adamf/Moros/shield/KiCad/3d_models/ab2_usb/stl/AB2_USB_MICRO_SMD.stl

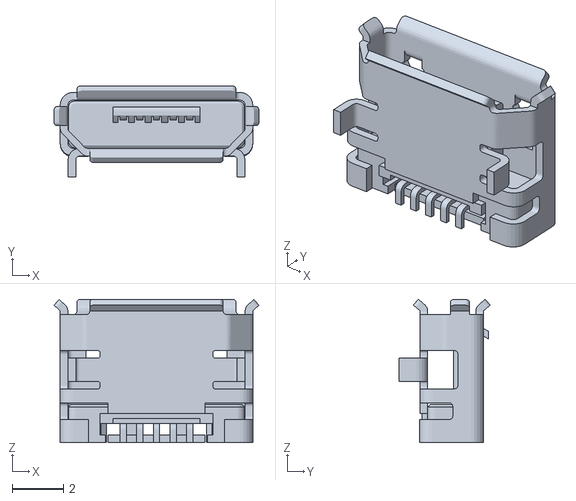
[picture p20: CAD file, 2014-12-30]
shield/KiCad/3d_models/ab2_usb/stl/AB2_USB_MICRO_SMD.stl
8.00 x 3.57 x 5.60
