adamf/Moros/shield/KiCad/3d_models/ab2_xtal/stl/AB2_XTAL_5.2x1.45x1.45MM.stl

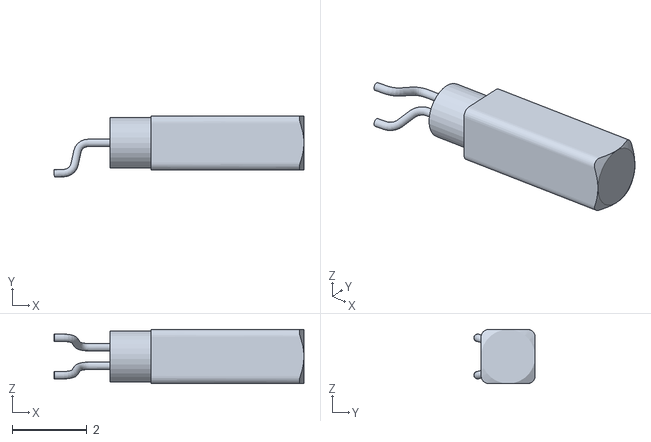
[picture p21: CAD file, 2014-12-30]
shield/KiCad/3d_models/ab2_xtal/stl/AB2_XTAL_5.2x1.45x1.45MM.stl
6.70 x 1.65 x 1.45
