adamf/Moros/shield/KiCad/3d_models/ab2_connector/stl/AB2_TRS_3p5MM_PTH_WINGS3D.stl

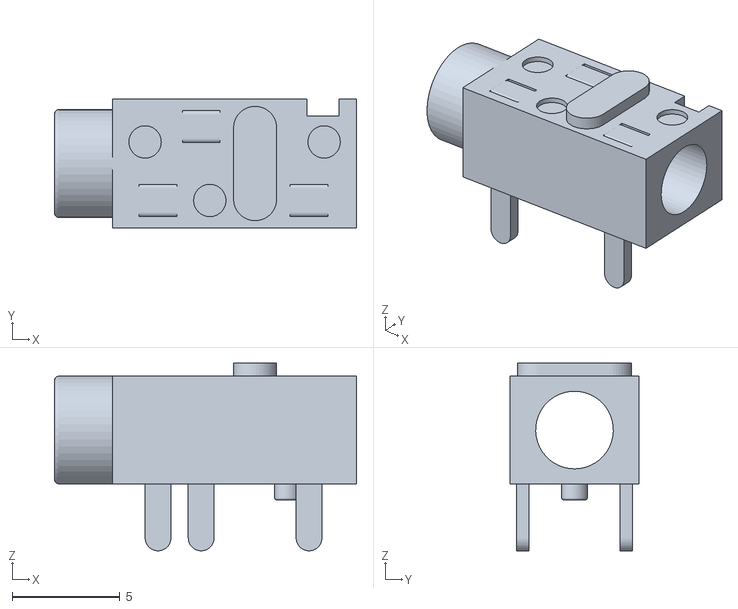
[picture p22: CAD file, 2014-12-30]
shield/KiCad/3d_models/ab2_connector/stl/AB2_TRS_3p5MM_PTH_WINGS3D.stl
14.0 x 6.00 x 8.70
