adamf/Moros/shield/KiCad/3d_models/ab2_header/stl/AB2_HDR_M01-1H_WINGS3D.stl

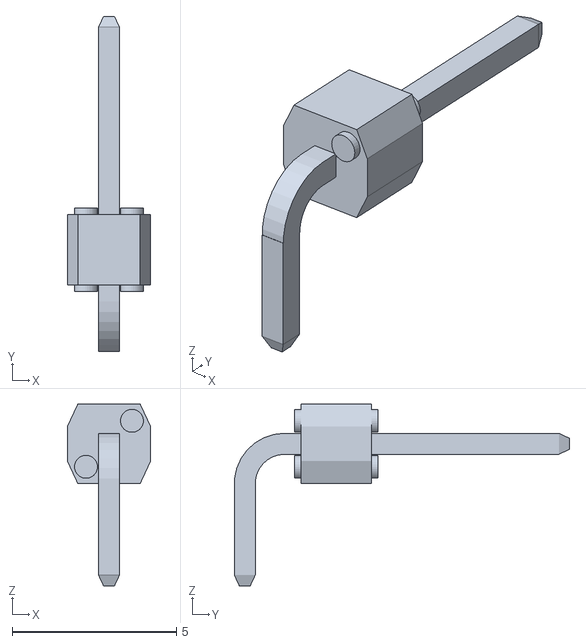
[picture p23: CAD file, 2014-12-30]
shield/KiCad/3d_models/ab2_header/stl/AB2_HDR_M01-1H_WINGS3D.stl
2.54 x 10.2 x 5.54
