adamf/Moros/shield/KiCad/3d_models/ab2_holesnpoles/stl/AB2_FR4_1.96x1.96INx1.6MM_ROUNDED_WINGS3D.stl

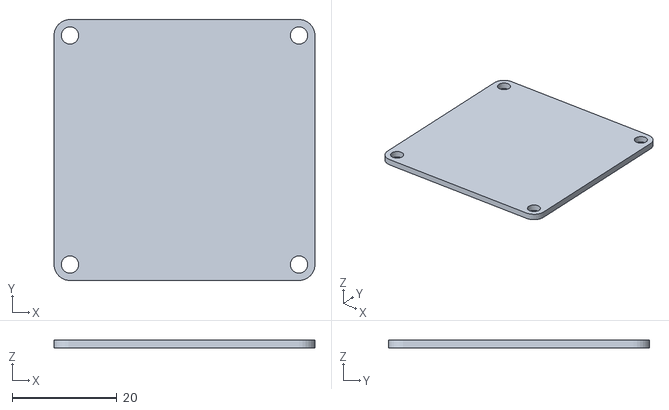
[picture p24: CAD file, 2014-12-30]
shield/KiCad/3d_models/ab2_holesnpoles/stl/AB2_FR4_1.96x1.96INx1.6MM_ROUNDED_WINGS3D.stl
49.8 x 49.8 x 1.55
