adamf/Moros/shield/KiCad/3d_models/ab2_input_devices/stl/AB2_PB_MOM_5.2MM_SMD.stl

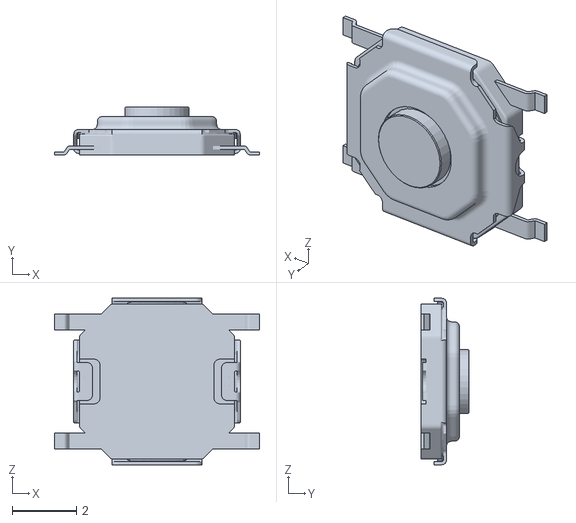
[picture p26: CAD file, 2014-12-30]
shield/KiCad/3d_models/ab2_input_devices/stl/AB2_PB_MOM_5.2MM_SMD.stl
6.40 x 1.50 x 5.20
