adamf/Moros/shield/KiCad/3d_models/ab2_lqfp/stl/AB2_LQFP80_WINGS3D.stl

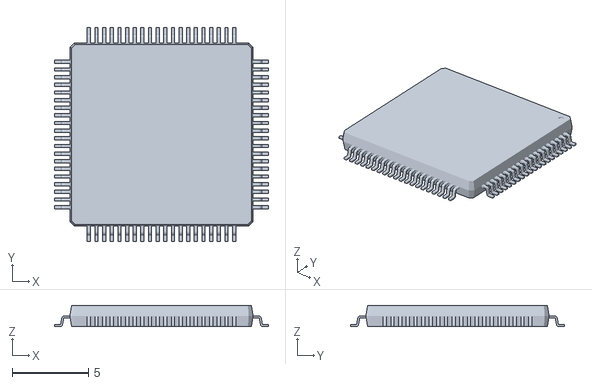
[picture p27: CAD file, 2014-12-30]
shield/KiCad/3d_models/ab2_lqfp/stl/AB2_LQFP80_WINGS3D.stl
14.0 x 14.0 x 1.40
