adamf/Moros/shield/KiCad/3d_models/ab2_power/stl/AB2_90DEG_4MM_JACK_PTH_WINGS3D.stl

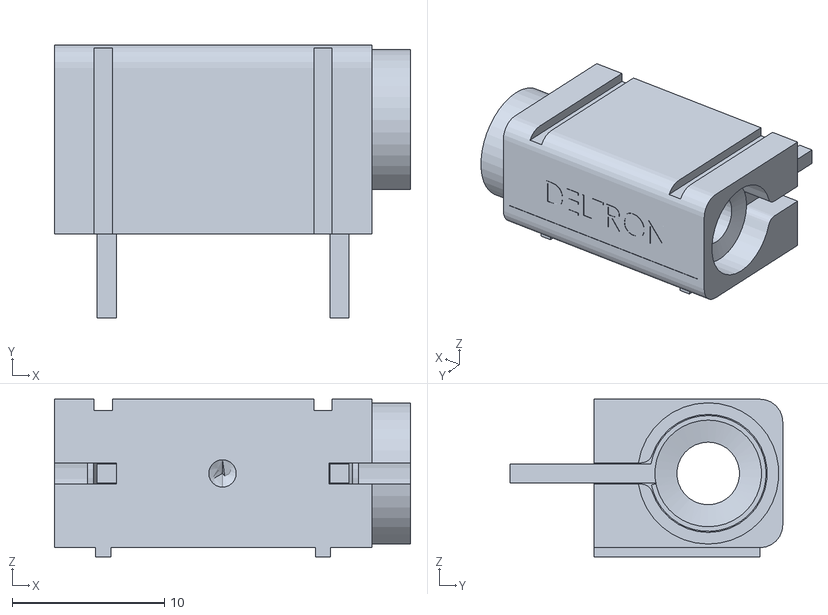
[picture p29: CAD file, 2014-12-30]
shield/KiCad/3d_models/ab2_power/stl/AB2_90DEG_4MM_JACK_PTH_WINGS3D.stl
23.4 x 17.9 x 10.4
