adamf/Moros/shield/KiCad/3d_models/ab2_usb/stl/AB2_USB_MINI_SMD.stl

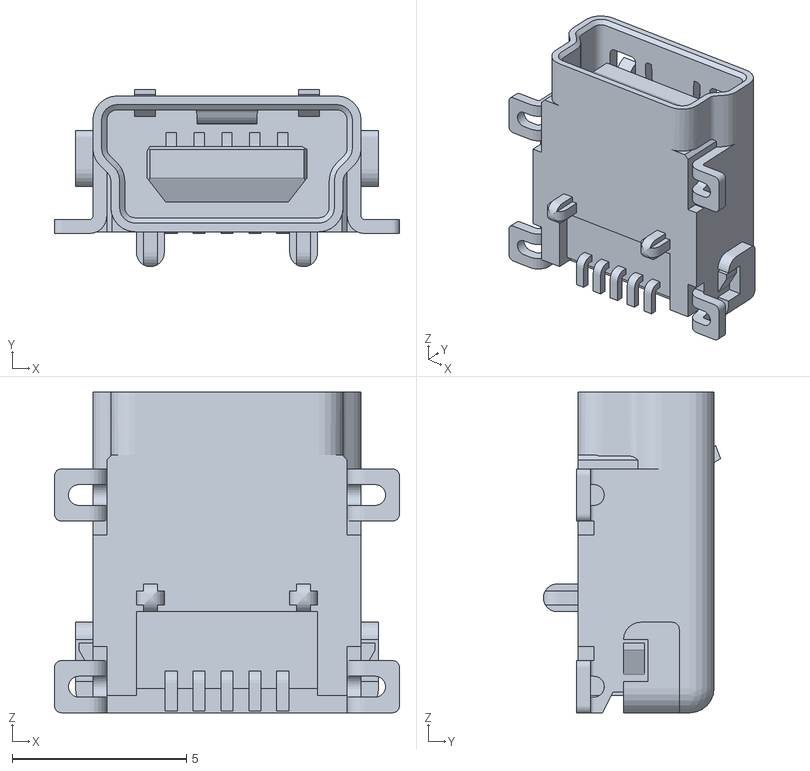
[picture p31: CAD file, 2014-12-30]
shield/KiCad/3d_models/ab2_usb/stl/AB2_USB_MINI_SMD.stl
9.90 x 5.09 x 9.20
