adamf/Moros/shield/KiCad/3d_models/ab2_7seg/stl/AB2_7SEG_5IN_H_WINGS3D.stl

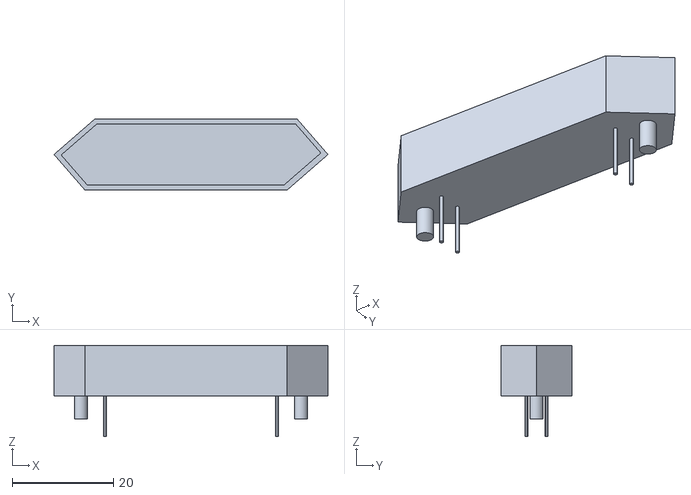
[picture p32: CAD file, 2014-12-30]
shield/KiCad/3d_models/ab2_7seg/stl/AB2_7SEG_5IN_H_WINGS3D.stl
54.1 x 14.0 x 18.0
