adamf/Moros/shield/KiCad/3d_models/ab2_connector/stl/AB2_DB25_F_RA.stl

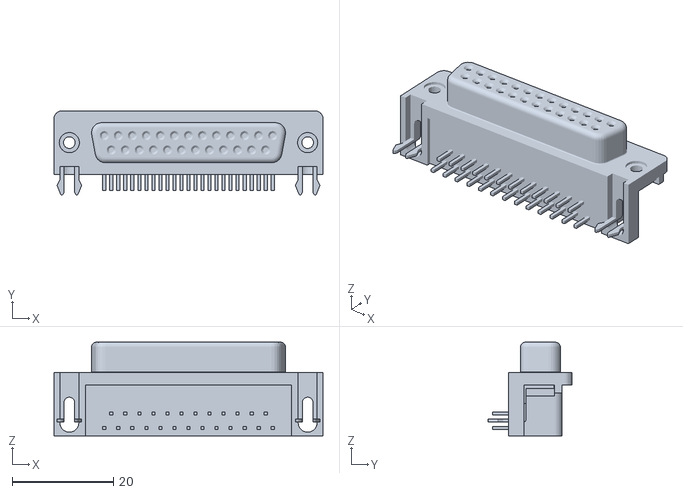
[picture p33: CAD file, 2014-12-30]
shield/KiCad/3d_models/ab2_connector/stl/AB2_DB25_F_RA.stl
53.1 x 16.6 x 18.5
