adamf/Moros/shield/KiCad/3d_models/ab2_holesnpoles/stl/AB2_FR4_1.96x0.94INx1.6MM_ROUNDED_WINGS3D.stl

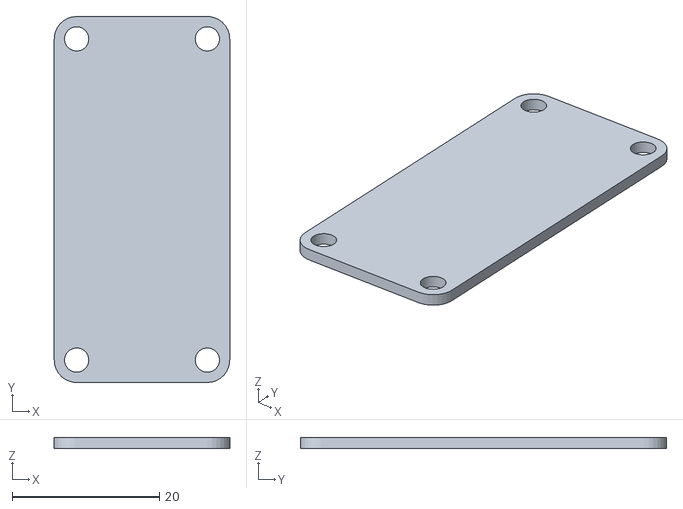
[picture p34: CAD file, 2014-12-30]
shield/KiCad/3d_models/ab2_holesnpoles/stl/AB2_FR4_1.96x0.94INx1.6MM_ROUNDED_WINGS3D.stl
23.9 x 49.8 x 1.55
