adamf/Moros/shield/KiCad/3d_models/ab2_idc/stl/AB2_HDR_M04-2V-S-TE_WINGS3D.stl

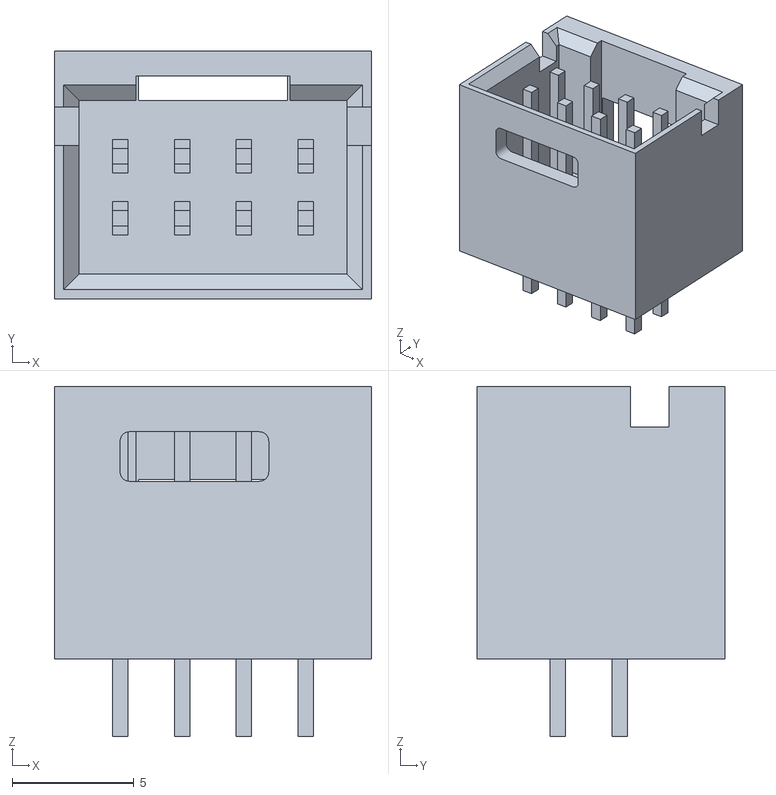
[picture p35: CAD file, 2014-12-30]
shield/KiCad/3d_models/ab2_idc/stl/AB2_HDR_M04-2V-S-TE_WINGS3D.stl
13.0 x 10.2 x 14.4
