adamf/Moros/shield/KiCad/3d_models/ab2_input_devices/stl/AB2_DIP_SW04_PIANO_PTH.stl

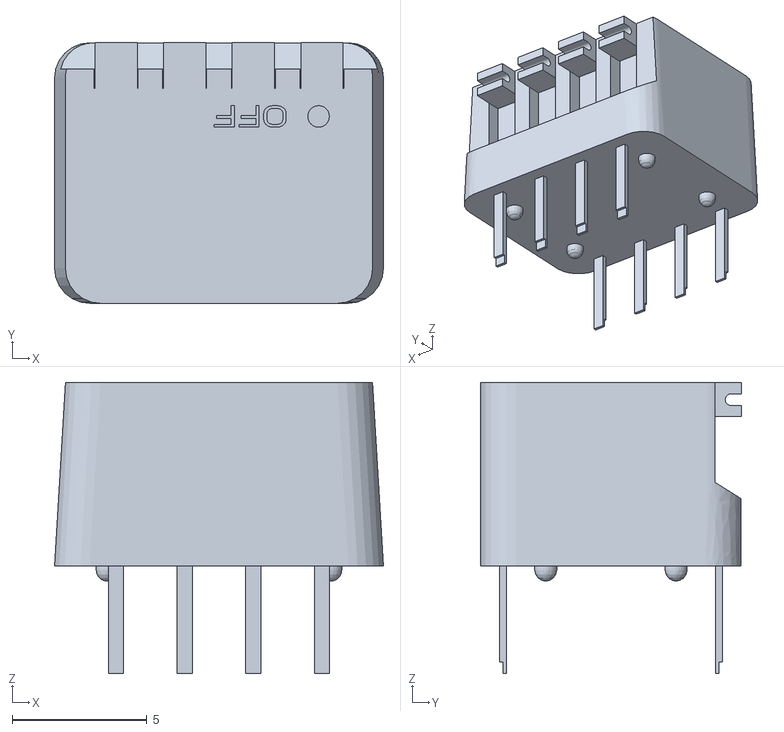
[picture p36: CAD file, 2014-12-30]
shield/KiCad/3d_models/ab2_input_devices/stl/AB2_DIP_SW04_PIANO_PTH.stl
12.2 x 9.65 x 10.8
