adamf/Moros/shield/KiCad/3d_models/ab2_lqfp/stl/AB2_LQFP64_WINGS3D.stl

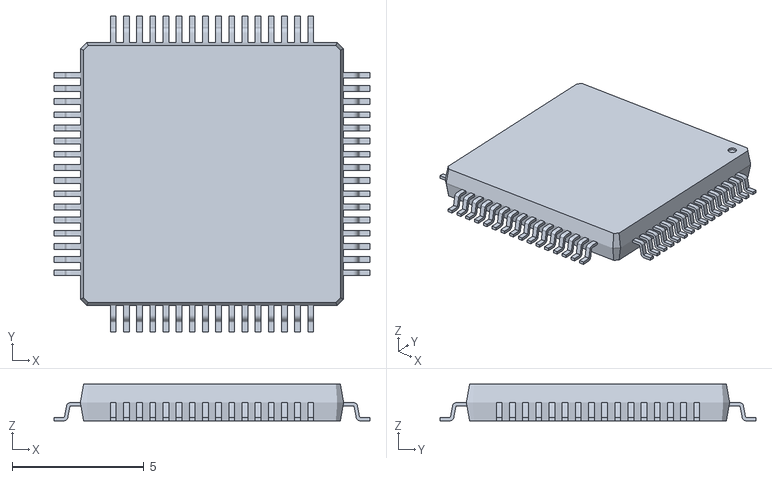
[picture p37: CAD file, 2014-12-30]
shield/KiCad/3d_models/ab2_lqfp/stl/AB2_LQFP64_WINGS3D.stl
12.0 x 12.0 x 1.40
