adamf/Moros/shield/KiCad/3d_models/ab2_passive/stl/AB2_0805_C_60_WINGS3D.stl

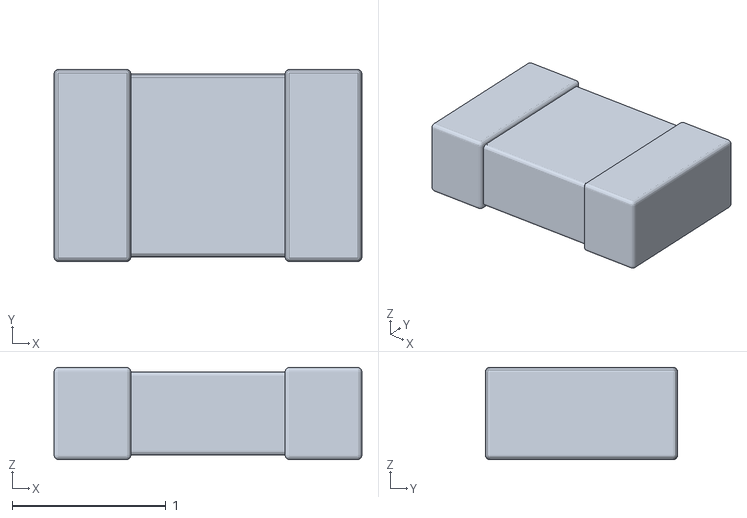
[picture p38: CAD file, 2014-12-30]
shield/KiCad/3d_models/ab2_passive/stl/AB2_0805_C_60_WINGS3D.stl
2.00 x 1.25 x 0.6
