adamf/Moros/shield/KiCad/3d_models/ab2_so/stl/AB2_SO16_WINGS3D.stl

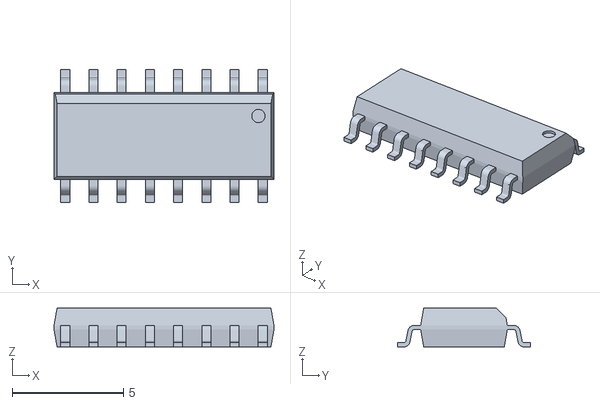
[picture p39: CAD file, 2014-12-30]
shield/KiCad/3d_models/ab2_so/stl/AB2_SO16_WINGS3D.stl
9.90 x 6.00 x 1.75
