adamf/Moros/shield/KiCad/3d_models/ab2_7seg/stl/AB2_7SEG_5IN_DEC_WINGS3D.stl

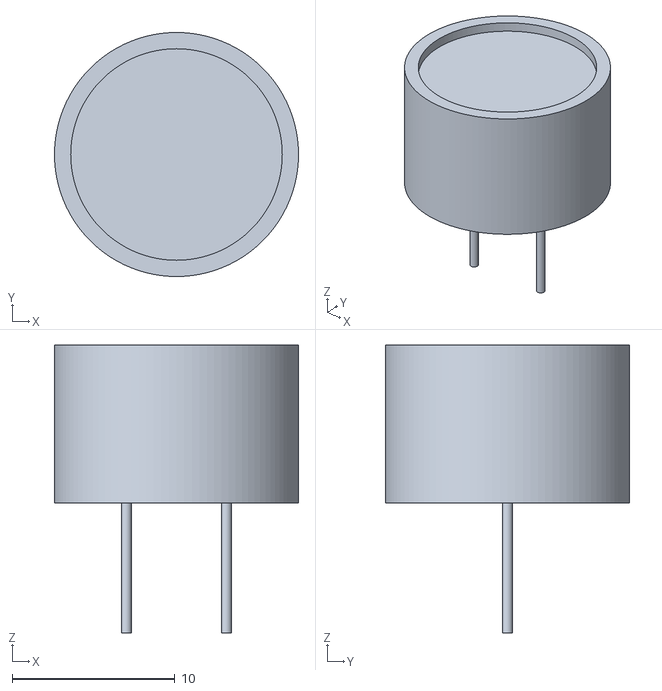
[picture p40: CAD file, 2014-12-30]
shield/KiCad/3d_models/ab2_7seg/stl/AB2_7SEG_5IN_DEC_WINGS3D.stl
15.0 x 15.0 x 17.7
