adamf/Moros/shield/KiCad/3d_models/ab2_connector/stl/AB2_RJ45_VERT_UNSHIELDED.stl

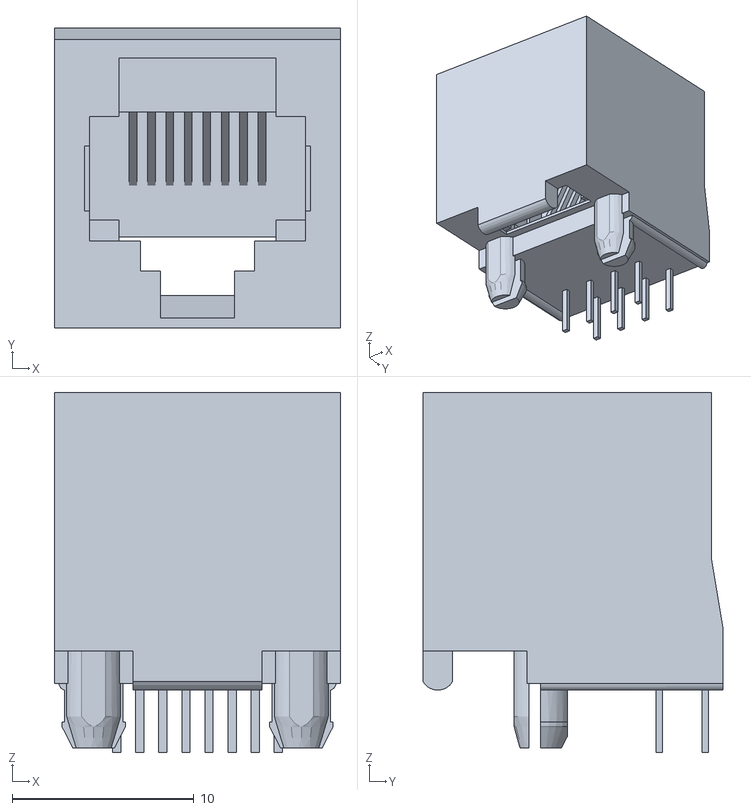
[picture p41: CAD file, 2014-12-30]
shield/KiCad/3d_models/ab2_connector/stl/AB2_RJ45_VERT_UNSHIELDED.stl
15.7 x 16.5 x 19.8
