adamf/Moros/shield/KiCad/3d_models/ab2_idc/stl/AB2_HDR_M07-2V-S-TE_WINGS3D.stl

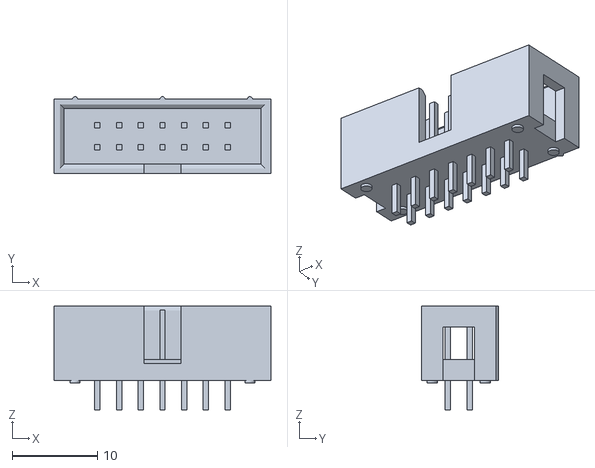
[picture p42: CAD file, 2014-12-30]
shield/KiCad/3d_models/ab2_idc/stl/AB2_HDR_M07-2V-S-TE_WINGS3D.stl
25.4 x 9.00 x 12.1
