adamf/Moros/shield/KiCad/3d_models/ab2_input_devices/stl/AB2_PB_MOM_6MM_PTH_BLK.stl

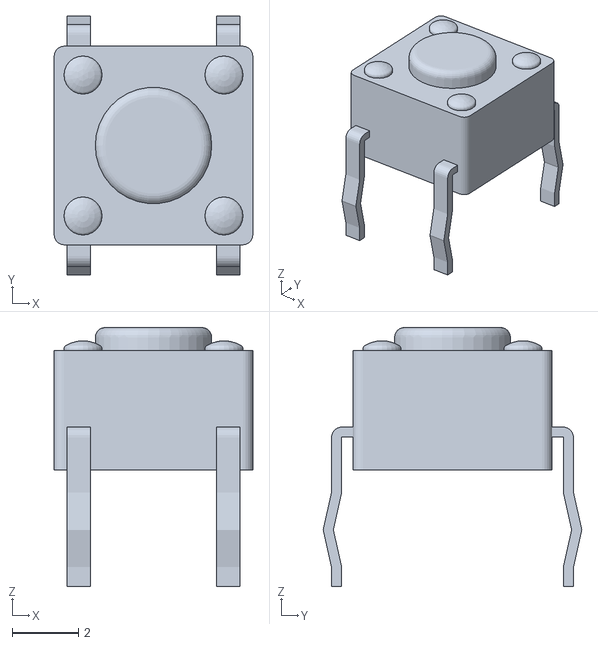
[picture p43: CAD file, 2014-12-30]
shield/KiCad/3d_models/ab2_input_devices/stl/AB2_PB_MOM_6MM_PTH_BLK.stl
5.99 x 7.80 x 7.81
