adamf/Moros/shield/KiCad/3d_models/ab2_lqfp/stl/AB2_LQFP100_WINGS3D.stl

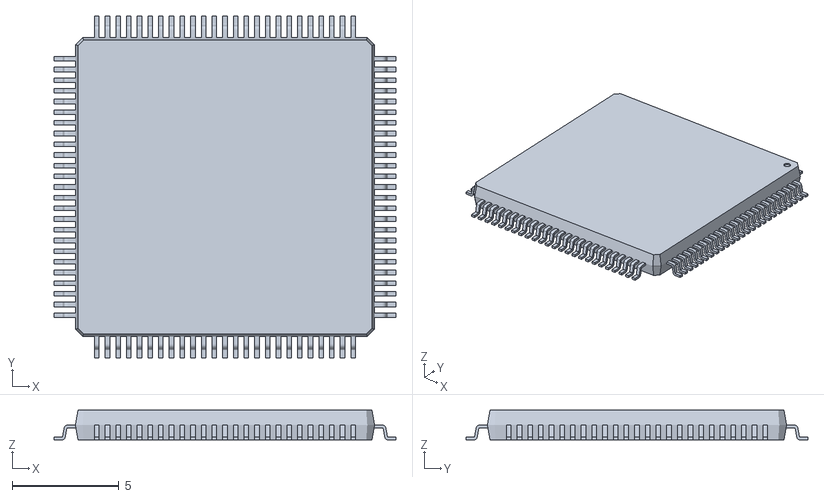
[picture p44: CAD file, 2014-12-30]
shield/KiCad/3d_models/ab2_lqfp/stl/AB2_LQFP100_WINGS3D.stl
16.0 x 16.0 x 1.40
