adamf/Moros/shield/KiCad/3d_models/ab2_passive/stl/AB2_L_RADIAL_8.7x12x5MM_SHORT_WINGS3D.stl

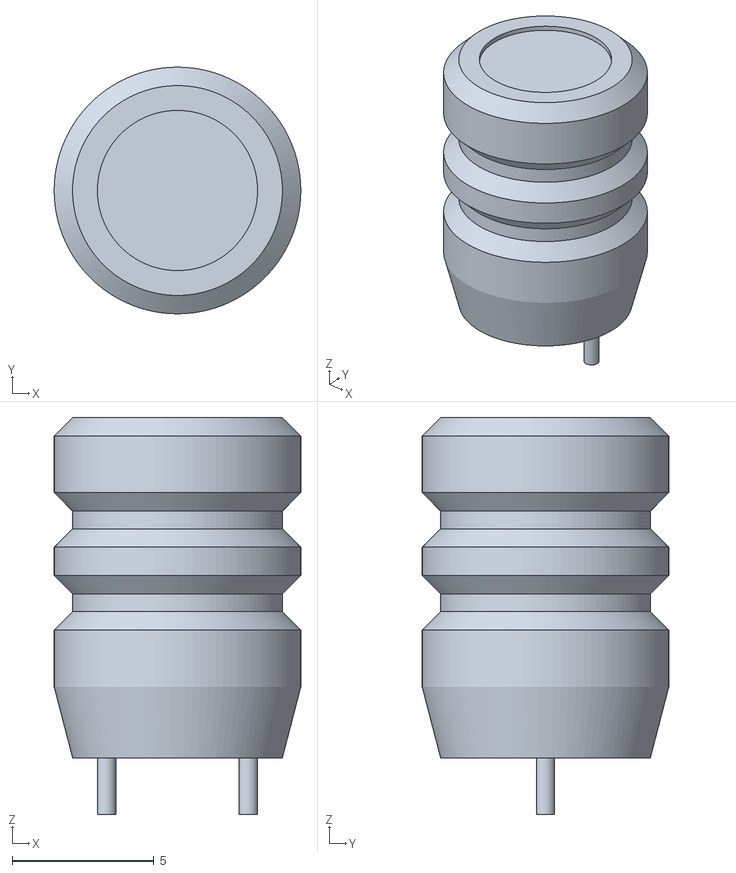
[picture p45: CAD file, 2014-12-30]
shield/KiCad/3d_models/ab2_passive/stl/AB2_L_RADIAL_8.7x12x5MM_SHORT_WINGS3D.stl
8.70 x 8.70 x 14.0
