adamf/Moros/shield/KiCad/3d_models/ab2_holesnpoles/stl/AB2_FR4_3.92x3.92INx1.6MM_ROUNDED_WINGS3D.stl

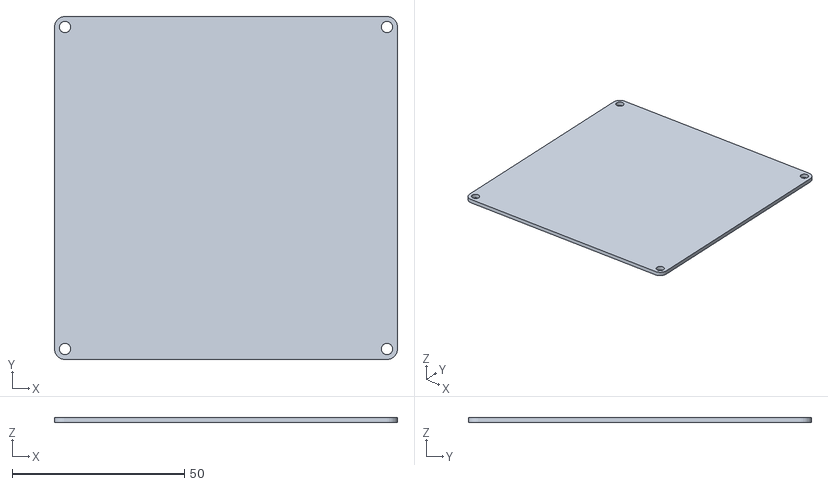
[picture p47: CAD file, 2014-12-30]
shield/KiCad/3d_models/ab2_holesnpoles/stl/AB2_FR4_3.92x3.92INx1.6MM_ROUNDED_WINGS3D.stl
99.6 x 99.6 x 1.55
