adamf/Moros/shield/KiCad/3d_models/ab2_idc/stl/AB2_HDR_M17-2V-S-OMRON.stl

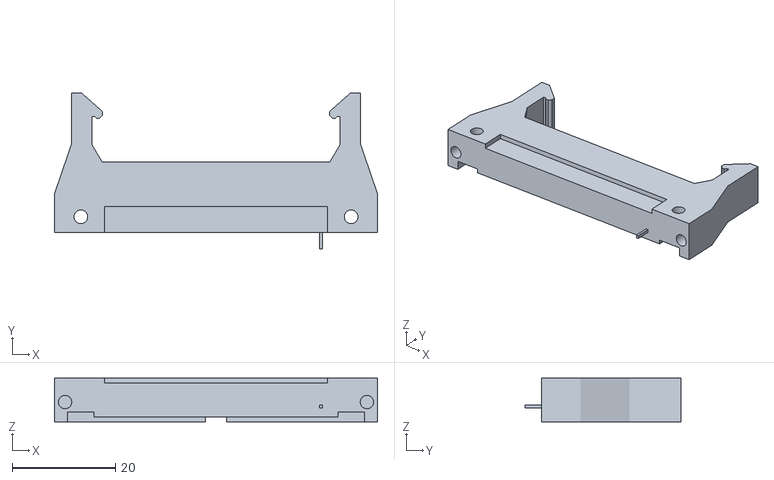
[picture p48: CAD file, 2014-12-30]
shield/KiCad/3d_models/ab2_idc/stl/AB2_HDR_M17-2V-S-OMRON.stl
62.5 x 30.2 x 8.50
