adamf/Moros/shield/KiCad/3d_models/ab2_lqfp/stl/AB2_LQFP32_WINGS3D.stl

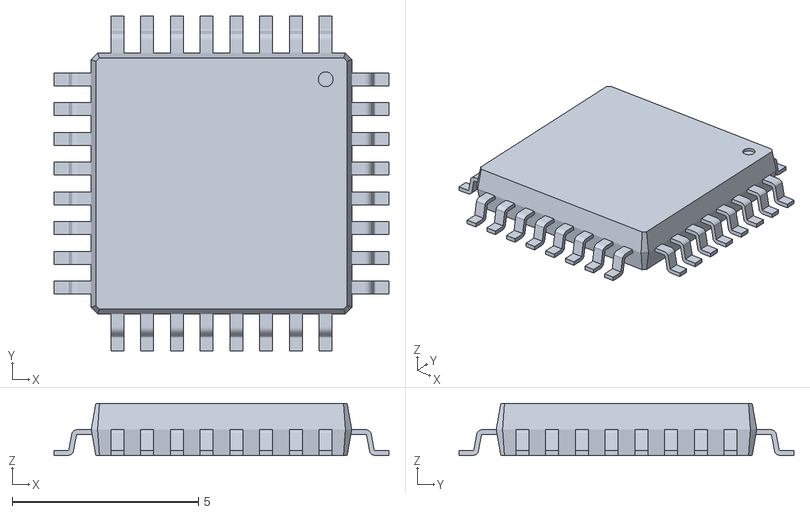
[picture p49: CAD file, 2014-12-30]
shield/KiCad/3d_models/ab2_lqfp/stl/AB2_LQFP32_WINGS3D.stl
9.00 x 9.00 x 1.40
