adamf/Moros/shield/KiCad/3d_models/ab2_passive/stl/AB2_1206_C_115_WINGS3D.stl

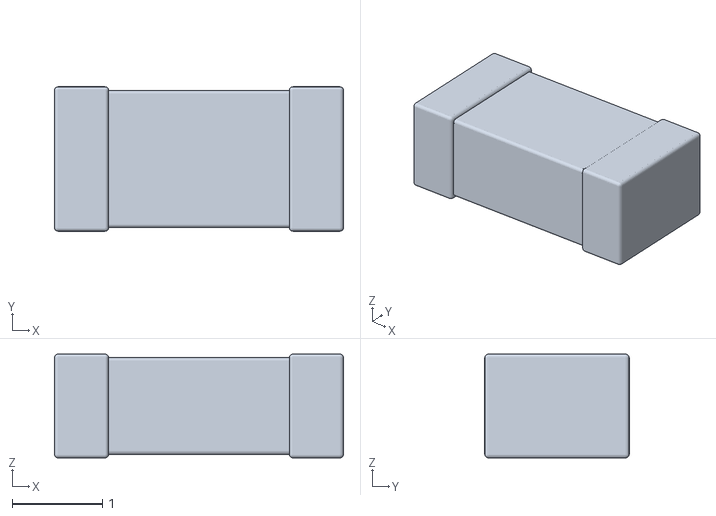
[picture p50: CAD file, 2014-12-30]
shield/KiCad/3d_models/ab2_passive/stl/AB2_1206_C_115_WINGS3D.stl
3.20 x 1.60 x 1.15
