adamf/Moros/shield/KiCad/3d_models/ab2_7seg/stl/AB2_7_SEG_8IN_DEC_WINGS3D.stl

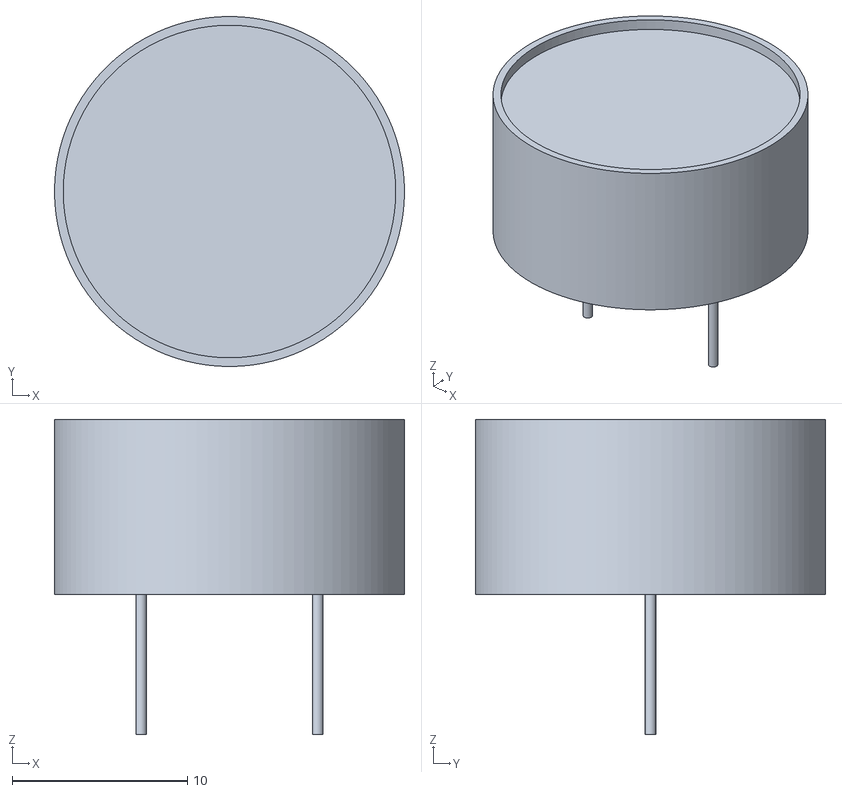
[picture p52: CAD file, 2014-12-30]
shield/KiCad/3d_models/ab2_7seg/stl/AB2_7_SEG_8IN_DEC_WINGS3D.stl
20.0 x 20.0 x 18.0
