adamf/Moros/shield/KiCad/3d_models/ab2_idc/stl/AB2_HDR_M05-2V-S-TE_WINGS3D.stl

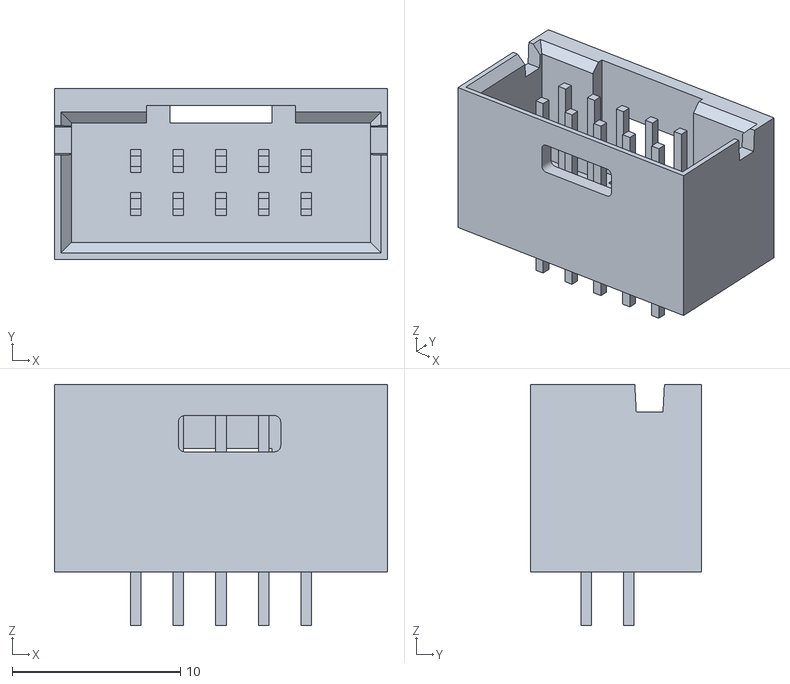
[picture p53: CAD file, 2014-12-30]
shield/KiCad/3d_models/ab2_idc/stl/AB2_HDR_M05-2V-S-TE_WINGS3D.stl
19.8 x 10.2 x 14.4
