adamf/Moros/shield/KiCad/3d_models/ab2_lqfp/stl/AB2_LQFP128_WINGS3D.stl

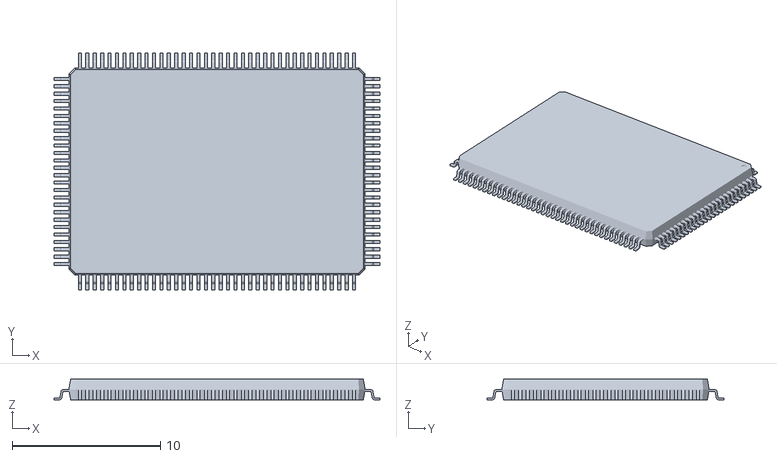
[picture p54: CAD file, 2014-12-30]
shield/KiCad/3d_models/ab2_lqfp/stl/AB2_LQFP128_WINGS3D.stl
22.0 x 16.0 x 1.40
