adamf/Moros/shield/KiCad/3d_models/ab2_passive/stl/AB2_DO-214AC_WINGS3D.stl

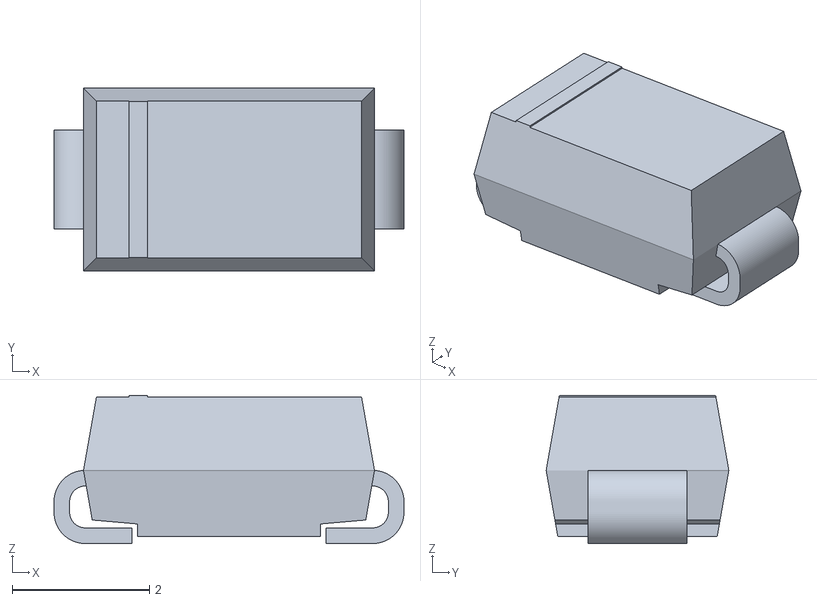
[picture p55: CAD file, 2014-12-30]
shield/KiCad/3d_models/ab2_passive/stl/AB2_DO-214AC_WINGS3D.stl
5.11 x 2.66 x 2.16
