adamf/Moros/shield/KiCad/3d_models/ab2_so/stl/AB2_SO18_W_WINGS3D.stl

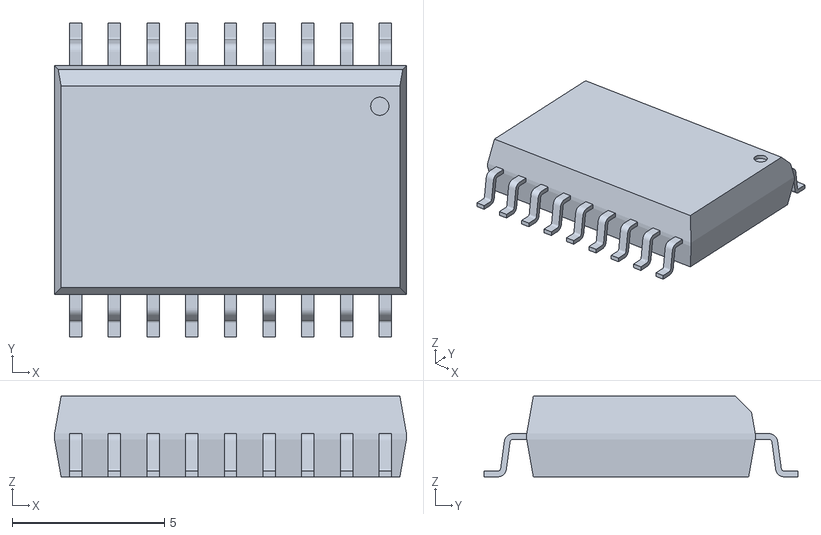
[picture p56: CAD file, 2014-12-30]
shield/KiCad/3d_models/ab2_so/stl/AB2_SO18_W_WINGS3D.stl
11.6 x 10.3 x 2.65
