adamf/Moros/shield/KiCad/3d_models/ab2_idc/stl/AB2_HDR_M03-2V-S-3M_WINGS3D.stl

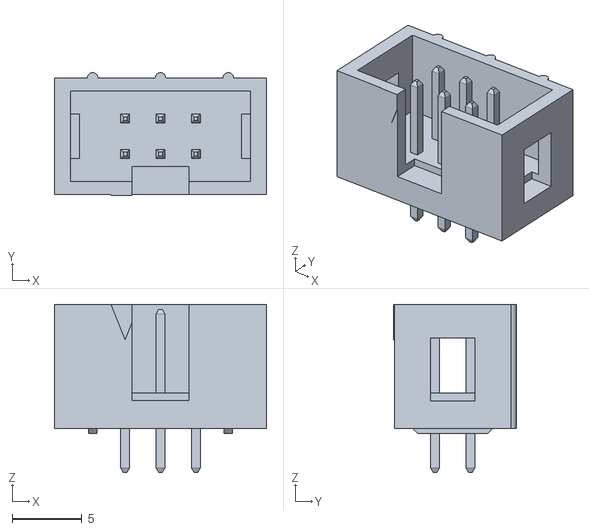
[picture p57: CAD file, 2014-12-30]
shield/KiCad/3d_models/ab2_idc/stl/AB2_HDR_M03-2V-S-3M_WINGS3D.stl
15.2 x 8.81 x 12.1
