adamf/Moros/shield/KiCad/3d_models/ab2_passive/stl/AB2_PLCC6_LED_ROUND_WINGS3D.stl

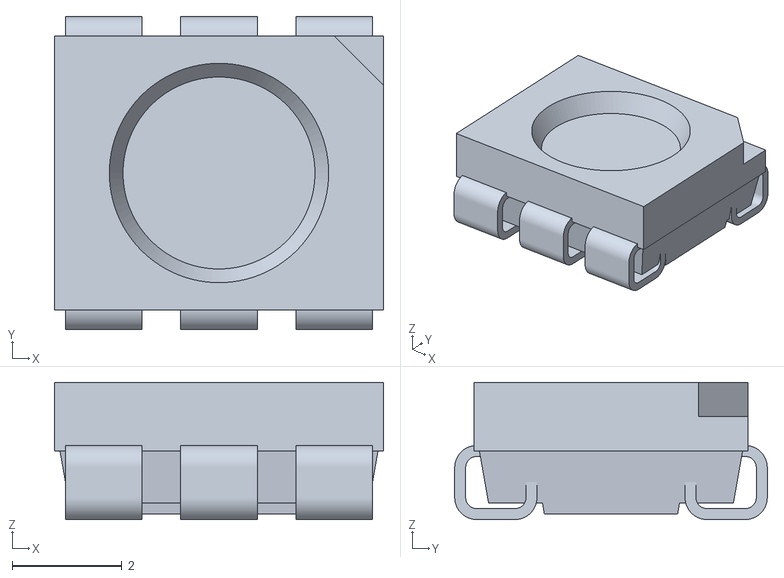
[picture p58: CAD file, 2014-12-30]
shield/KiCad/3d_models/ab2_passive/stl/AB2_PLCC6_LED_ROUND_WINGS3D.stl
6.00 x 5.70 x 2.50
