adamf/Moros/shield/KiCad/3d_models/ab2_so/stl/AB2_SO16_W_WINGS3D.stl

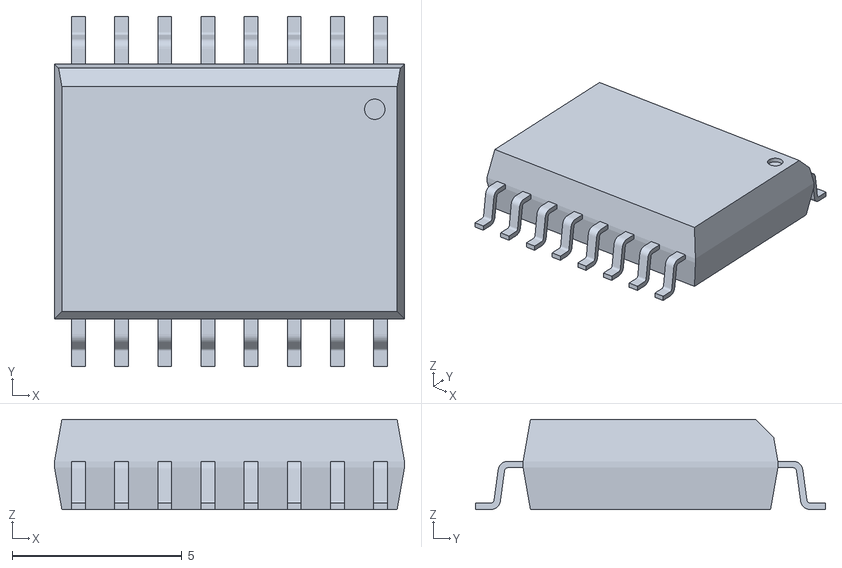
[picture p62: CAD file, 2014-12-30]
shield/KiCad/3d_models/ab2_so/stl/AB2_SO16_W_WINGS3D.stl
10.3 x 10.3 x 2.65
