adamf/Moros/shield/KiCad/3d_models/ab2_idc/stl/AB2_HDR_M01-1V-BARE-16p2-13_WINGS3D.stl

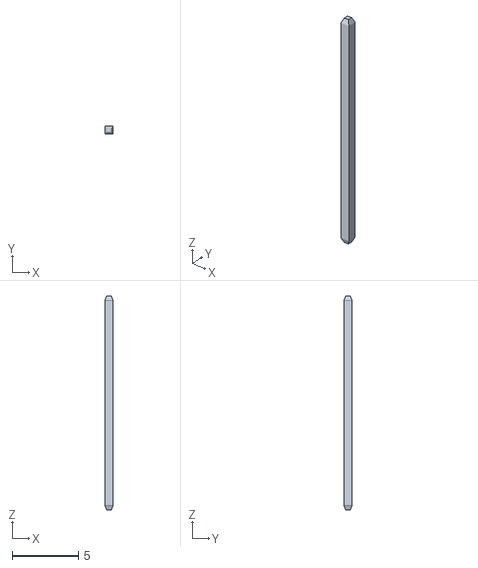
[picture p63: CAD file, 2014-12-30]
shield/KiCad/3d_models/ab2_idc/stl/AB2_HDR_M01-1V-BARE-16p2-13_WINGS3D.stl
0.64 x 0.64 x 16.2
