adamf/Moros/shield/KiCad/3d_models/ab2_passive/stl/AB2_0402_C_50_WINGS3D.stl

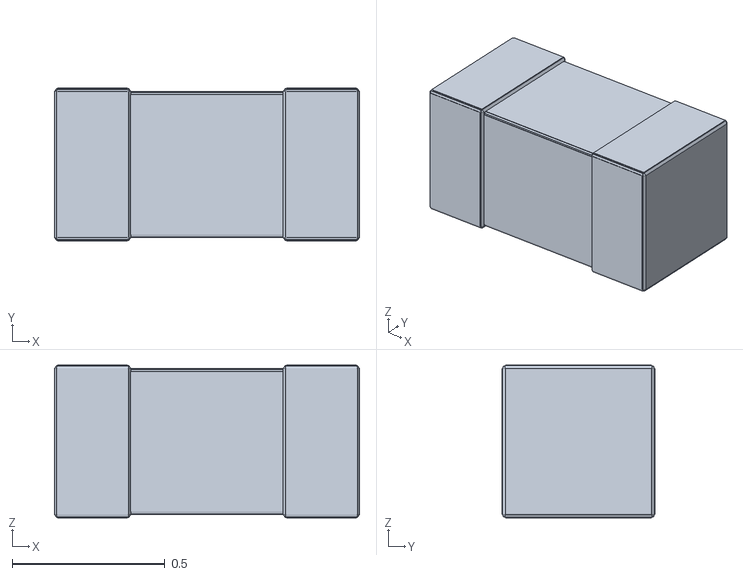
[picture p64: CAD file, 2014-12-30]
shield/KiCad/3d_models/ab2_passive/stl/AB2_0402_C_50_WINGS3D.stl
1.00 x 0.5 x 0.5
