adamf/Moros/shield/KiCad/3d_models/ab2_so/stl/AB2_SO14_W_WINGS3D.stl

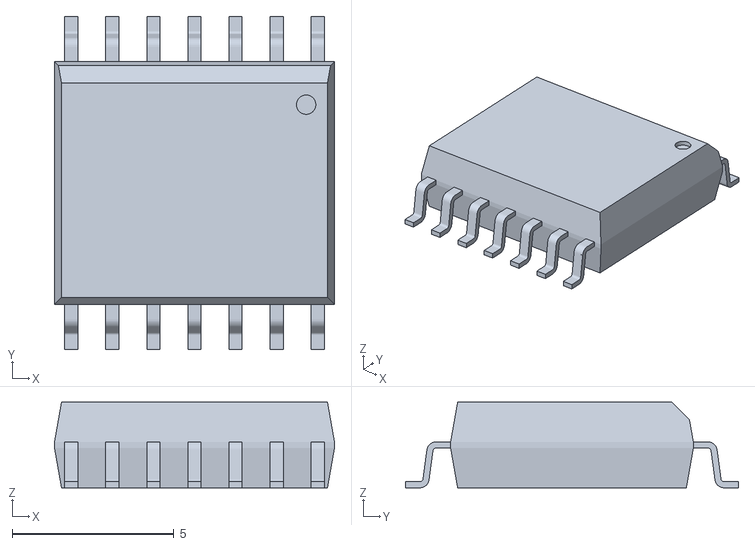
[picture p65: CAD file, 2014-12-30]
shield/KiCad/3d_models/ab2_so/stl/AB2_SO14_W_WINGS3D.stl
8.65 x 10.3 x 2.65
