adamf/Moros/shield/KiCad/3d_models/ab2_idc/stl/AB2_HDR_M05-2V-S-3M_WINGS3D.stl

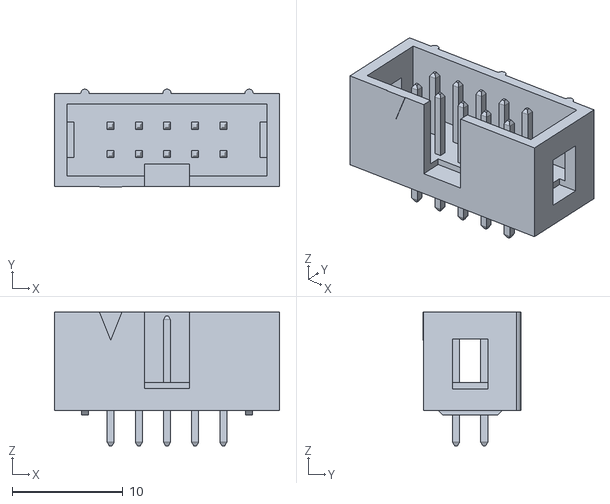
[picture p66: CAD file, 2014-12-30]
shield/KiCad/3d_models/ab2_idc/stl/AB2_HDR_M05-2V-S-3M_WINGS3D.stl
20.3 x 8.81 x 12.1
