adamf/Moros/shield/KiCad/3d_models/ab2_passive/stl/AB2_2010_R_WINGS3D.stl

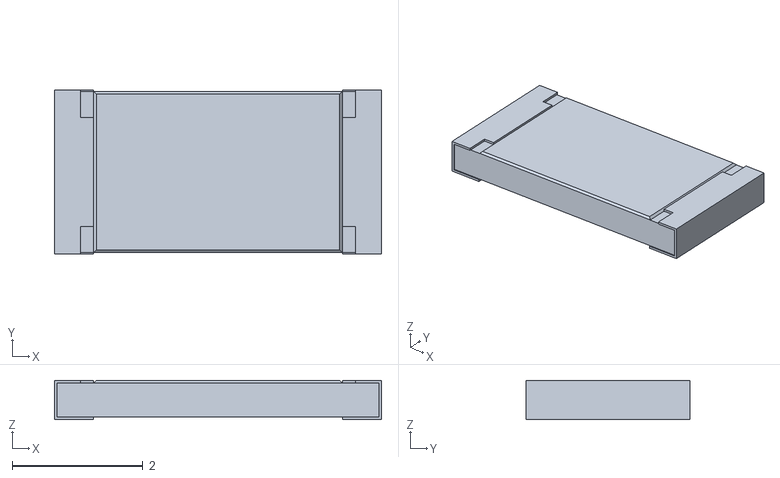
[picture p68: CAD file, 2014-12-30]
shield/KiCad/3d_models/ab2_passive/stl/AB2_2010_R_WINGS3D.stl
5.00 x 2.50 x 0.6
