adamf/Moros/shield/KiCad/3d_models/ab2_idc/stl/AB2_HDR_M17-2V-BARE-16p2-13_WINGS3D.stl

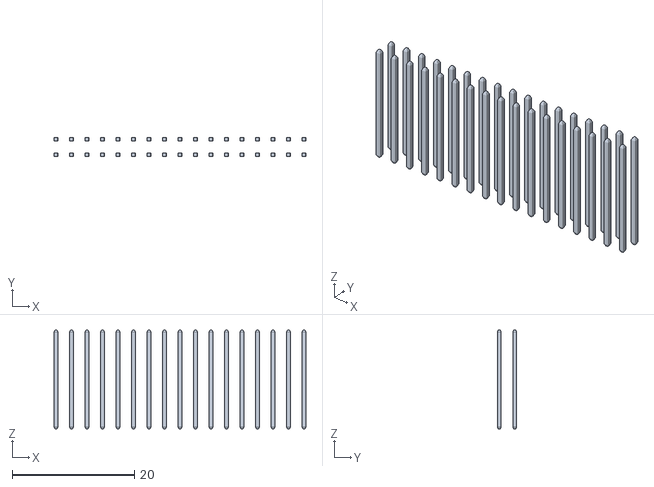
[picture p69: CAD file, 2014-12-30]
shield/KiCad/3d_models/ab2_idc/stl/AB2_HDR_M17-2V-BARE-16p2-13_WINGS3D.stl
41.3 x 3.18 x 16.2
