adamf/Moros/shield/KiCad/3d_models/ab2_passive/stl/AB2_0805_R_WINGS3D.stl

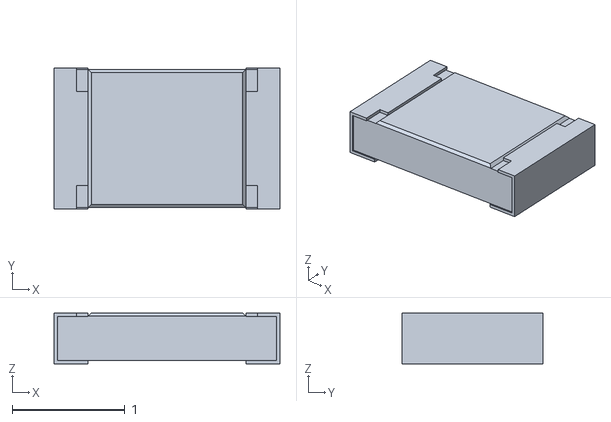
[picture p71: CAD file, 2014-12-30]
shield/KiCad/3d_models/ab2_passive/stl/AB2_0805_R_WINGS3D.stl
2.00 x 1.25 x 0.45
