adamf/Moros/shield/KiCad/3d_models/ab2_passive/stl/AB2_DO-214AB_WINGS3D.stl

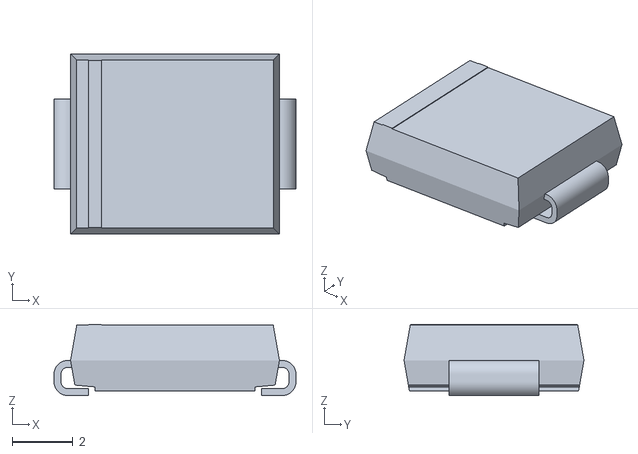
[picture p72: CAD file, 2014-12-30]
shield/KiCad/3d_models/ab2_passive/stl/AB2_DO-214AB_WINGS3D.stl
7.94 x 5.91 x 2.34
