adamf/Moros/shield/KiCad/3d_models/ab2_passive/stl/AB2_2043_R_WINGS3D.stl

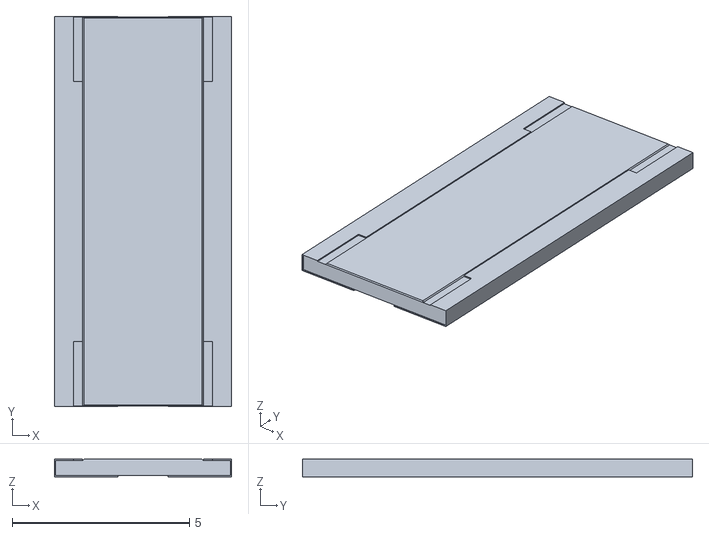
[picture p73: CAD file, 2014-12-30]
shield/KiCad/3d_models/ab2_passive/stl/AB2_2043_R_WINGS3D.stl
5.00 x 11.0 x 0.5
