adamf/Moros/shield/KiCad/3d_models/ab2_passive/stl/AB2_2512_R_WINGS3D.stl

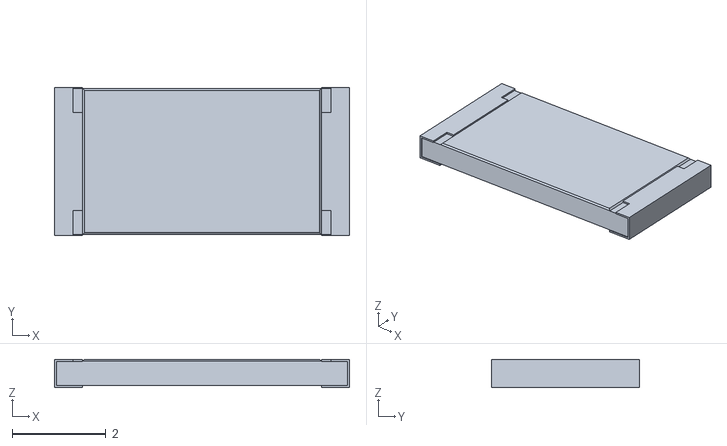
[picture p74: CAD file, 2014-12-30]
shield/KiCad/3d_models/ab2_passive/stl/AB2_2512_R_WINGS3D.stl
6.30 x 3.15 x 0.6
