adamf/Moros/shield/KiCad/3d_models/ab2_passive/stl/AB2_0402_R_WINGS3D.stl

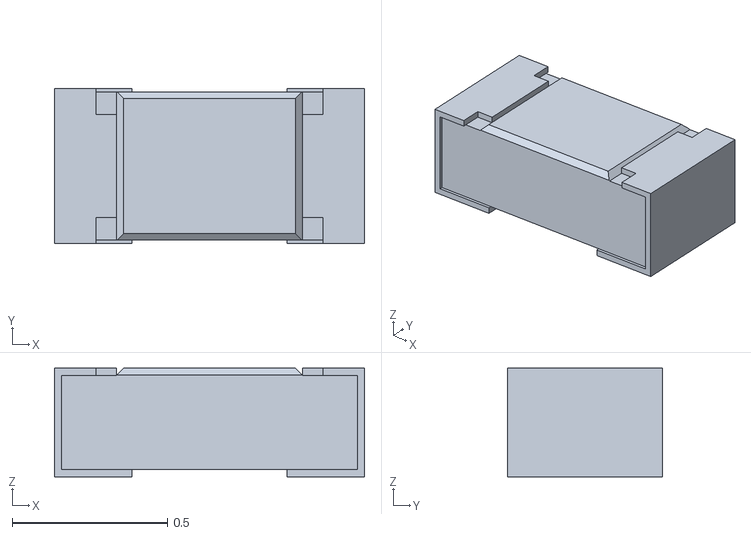
[picture p75: CAD file, 2014-12-30]
shield/KiCad/3d_models/ab2_passive/stl/AB2_0402_R_WINGS3D.stl
1.00 x 0.5 x 0.35
