adamf/Moros/shield/KiCad/3d_models/ab2_passive/stl/AB2_1210_R_WINGS3D.stl

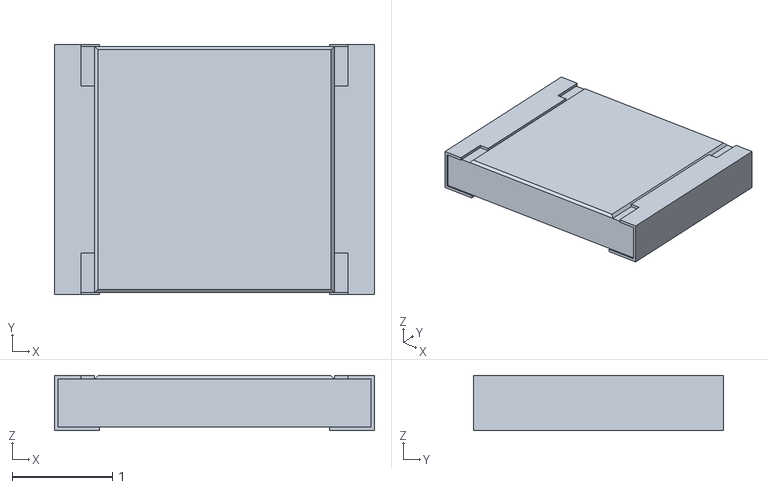
[picture p76: CAD file, 2014-12-30]
shield/KiCad/3d_models/ab2_passive/stl/AB2_1210_R_WINGS3D.stl
3.20 x 2.50 x 0.55
