adamf/Moros/shield/KiCad/3d_models/ab2_passive/stl/AB2_0603_R_WINGS3D.stl

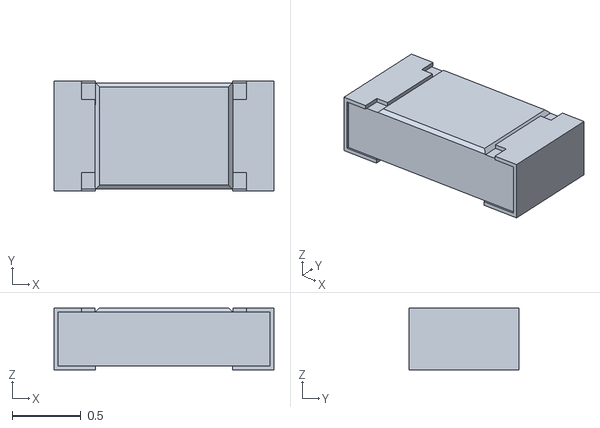
[picture p82: CAD file, 2014-12-30]
shield/KiCad/3d_models/ab2_passive/stl/AB2_0603_R_WINGS3D.stl
1.60 x 0.8 x 0.45
