adamf/Moros/shield/KiCad/3d_models/ab2_passive/stl/AB2_1206_C_80_WINGS3D.stl

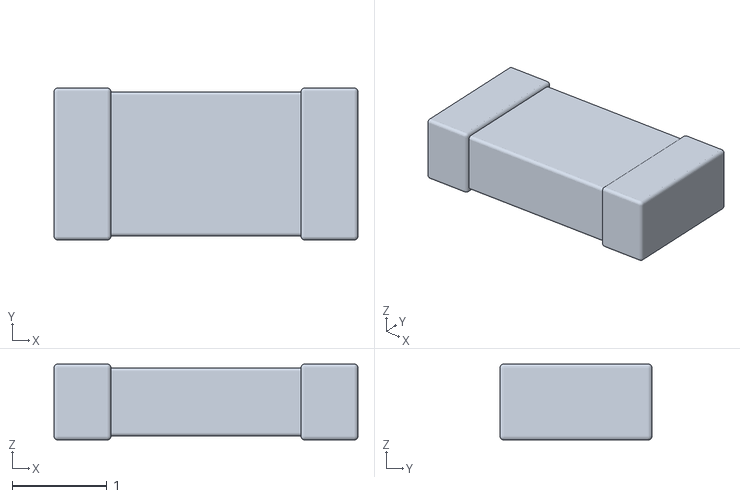
[picture p84: CAD file, 2014-12-30]
shield/KiCad/3d_models/ab2_passive/stl/AB2_1206_C_80_WINGS3D.stl
3.20 x 1.60 x 0.8
