adamf/Moros/shield/KiCad/3d_models/ab2_passive/stl/AB2_1210_C_160_WINGS3D.stl

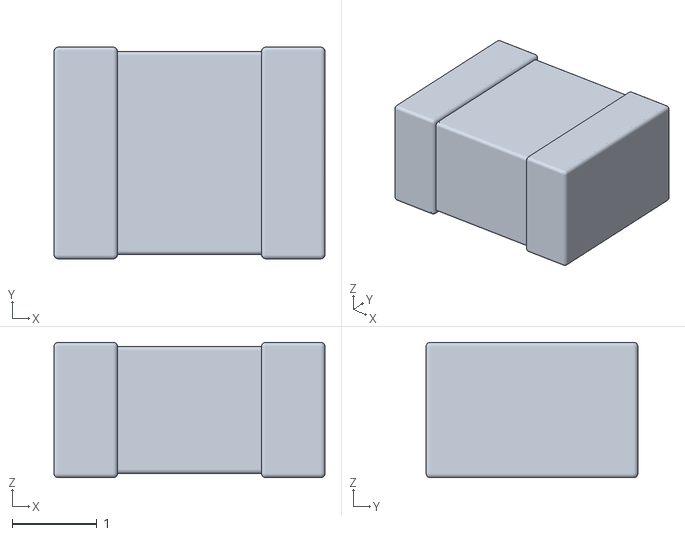
[picture p85: CAD file, 2014-12-30]
shield/KiCad/3d_models/ab2_passive/stl/AB2_1210_C_160_WINGS3D.stl
3.20 x 2.50 x 1.60
