adamf/Moros/moros/cccp_flag.h

// Generated with bin2header.py by Freetronics
// Source file name: cccp_flag.bmp

#include <stdint.h>

#ifdef __AVR__
#define _PGM_ PROGMEM
#else
#define _PGM_
#endif



static const uint8_t cccp_flag[] _PGM_ = {
    /* 0x0000: */ 0x42, 0x4d, 0x06, 0x08, 0x00, 0x00, 0x00, 0x00, 0x00, 0x00, 0x86, 0x00, 0x00, 0x00, 0x6c, 0x00,
    /* 0x0010: */ 0x00, 0x00, 0x4d, 0x00, 0x00, 0x00, 0x30, 0x00, 0x00, 0x00, 0x01, 0x00, 0x04, 0x00, 0x00, 0x00,
    /* 0x0020: */ 0x00, 0x00, 0x80, 0x07, 0x00, 0x00, 0x13, 0x0b, 0x00, 0x00, 0x13, 0x0b, 0x00, 0x00, 0x03, 0x00,
    /* 0x0030: */ 0x00, 0x00, 0x03, 0x00, 0x00, 0x00, 0x42, 0x47, 0x52, 0x73, 0x00, 0x00, 0x00, 0x00, 0x00, 0x00,
    /* 0x0040: */ 0x00, 0x00, 0x00, 0x00, 0x00, 0x00, 0x00, 0x00, 0x00, 0x00, 0x00, 0x00, 0x00, 0x00, 0x00, 0x00,
    /* 0x0050: */ 0x00, 0x00, 0x00, 0x00, 0x00, 0x00, 0x00, 0x00, 0x00, 0x00, 0x00, 0x00, 0x00, 0x00, 0x00, 0x00,
    /* 0x0060: */ 0x00, 0x00, 0x00, 0x00, 0x00, 0x00, 0x00, 0x00, 0x00, 0x00, 0x02, 0x00, 0x00, 0x00, 0x00, 0x00,
    /* 0x0070: */ 0x00, 0x00, 0x00, 0x00, 0x00, 0x00, 0x00, 0x00, 0x00, 0x00, 0x0a, 0xdf, 0xff, 0x00, 0x00, 0x00,
    /* 0x0080: */ 0x8d, 0x00, 0x00, 0x00, 0xc8, 0x00, 0x22, 0x22, 0x22, 0x22, 0x22, 0x22, 0x11, 0x11, 0x11, 0x11,
    /* 0x0090: */ 0x22, 0x22, 0x22, 0x21, 0x11, 0x11, 0x22, 0x22, 0x11, 0x12, 0x22, 0x21, 0x12, 0x22, 0x11, 0x22,
    /* 0x00a0: */ 0x11, 0x22, 0x11, 0x22, 0x11, 0x22, 0x21, 0x12, 0x22, 0x11, 0x22, 0x22, 0x10, 0x00, 0x11, 0x12,
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
    /* 0x0260: */ 0x22, 0x22, 0x11, 0x22, 0x20, 0x00, 0x11, 0x11, 0x12, 0x22, 0x22, 0x22, 0x22, 0x22, 0x22, 0x22,
    /* 0x0270: */ 0x22, 0x11, 0x11, 0x11, 0x12, 0x22, 0x22, 0x22, 0x11, 0x12, 0x22, 0x22, 0x00, 0x22, 0x22, 0x20,
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

};
