adamf/Moros/moros/printf.cpp

#include <Arduino.h>
#include <stdio.h>
#include <stdarg.h>
void serprintf(const char *fmt, ... ){
        char buf[128]; // resulting string limited to 128 chars
        va_list args;
        va_start (args, fmt );
        vsnprintf(buf, 128, fmt, args);
        va_end (args);
        Serial.print(buf);
}
